SebastianEspende/PROYECTOCNC/3d/v2/agarremotor.SLDPRT

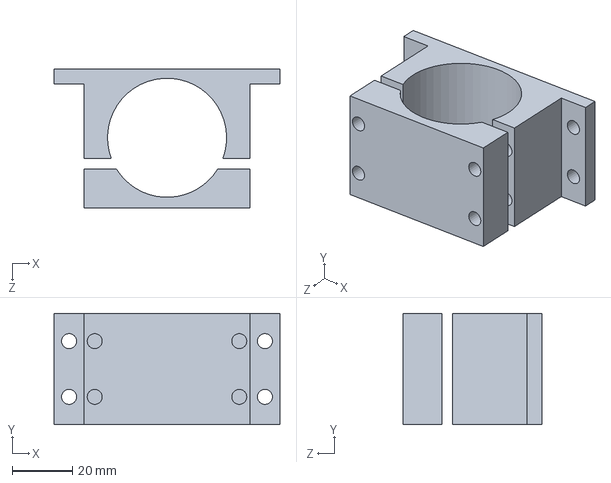
[picture p49: CAD file, 2024-12-08]
3d/v2/agarremotor.SLDPRT
75.0 x 37.0 x 46.2 mm
