SebastianEspende/PROYECTOCNC/3d/Y.SLDPRT

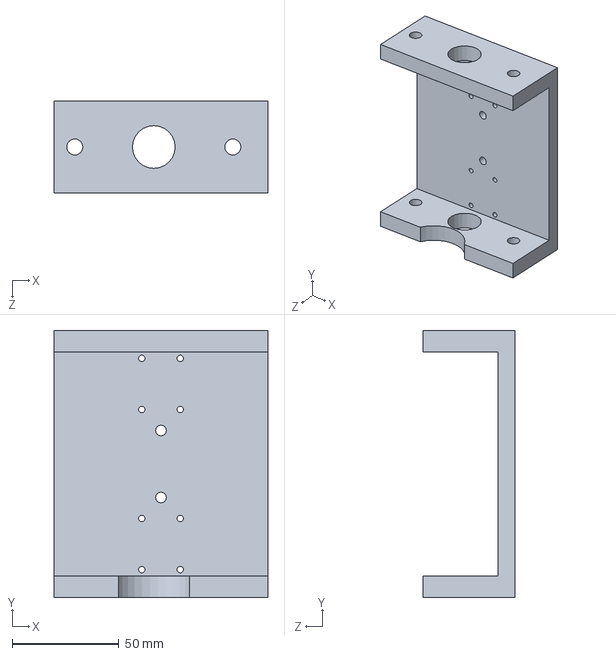
[picture p50: CAD file, 2024-12-08]
3d/Y.SLDPRT
100.0 x 125.0 x 43.0 mm
