SebastianEspende/PROYECTOCNC/3d/FRONTAL_BASE.SLDPRT

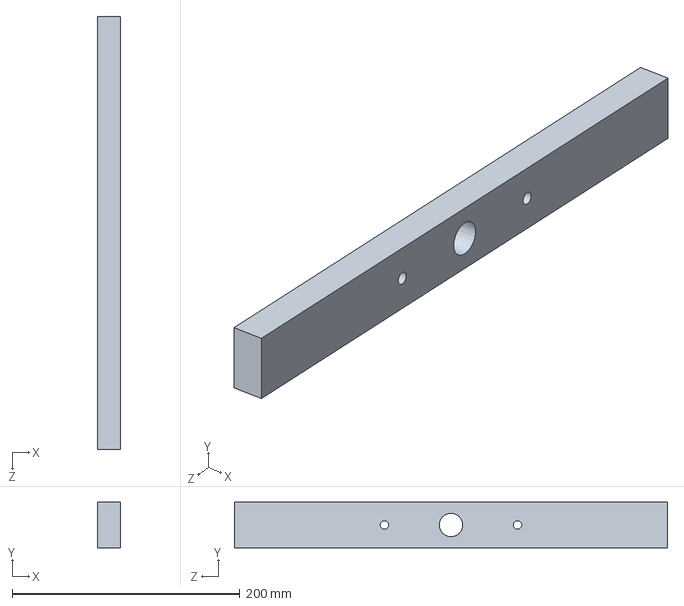
[picture p51: CAD file, 2024-12-08]
3d/FRONTAL_BASE.SLDPRT
20.0 x 40.0 x 380.0 mm
