SebastianEspende/PROYECTOCNC/3d/v2/soportenema17.SLDPRT

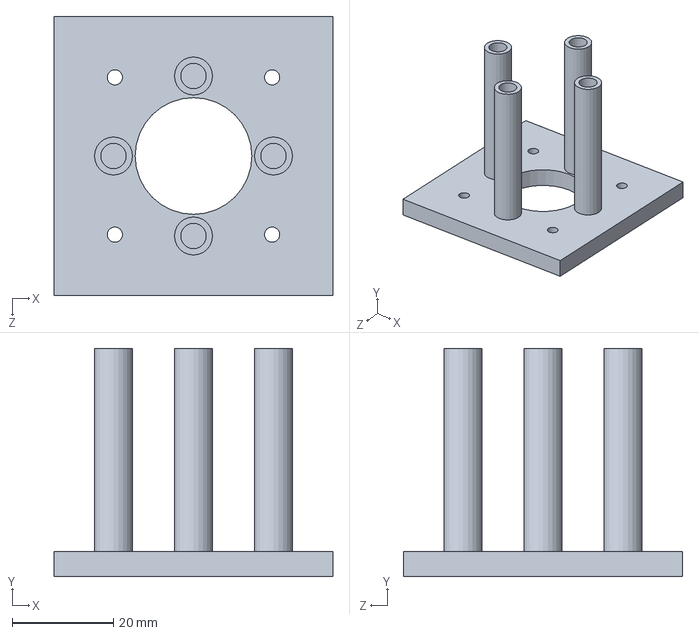
[picture p52: CAD file, 2024-12-08]
3d/v2/soportenema17.SLDPRT
55.0 x 45.0 x 55.0 mm
