SebastianEspende/PROYECTOCNC/3d/BASE.SLDPRT

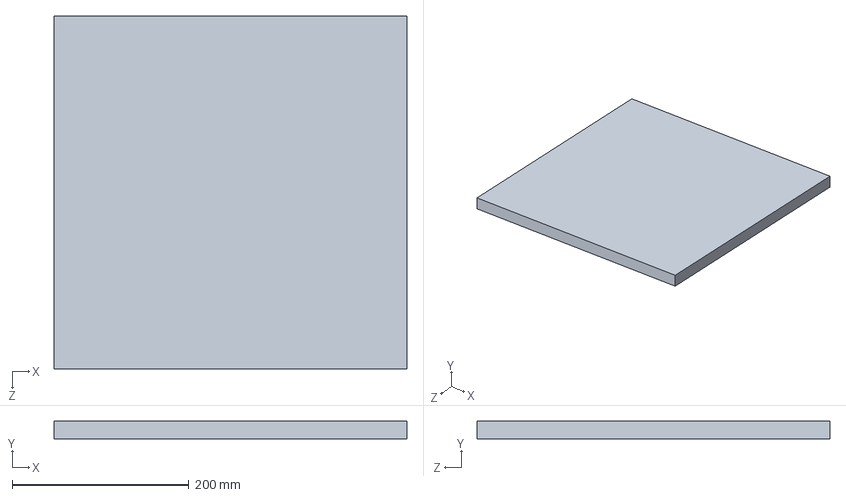
[picture p53: CAD file, 2024-12-04]
3d/BASE.SLDPRT
400.0 x 20.0 x 400.0 mm
