SebastianEspende/PROYECTOCNC/3d/v2/varilla_enroscada_Z.SLDPRT

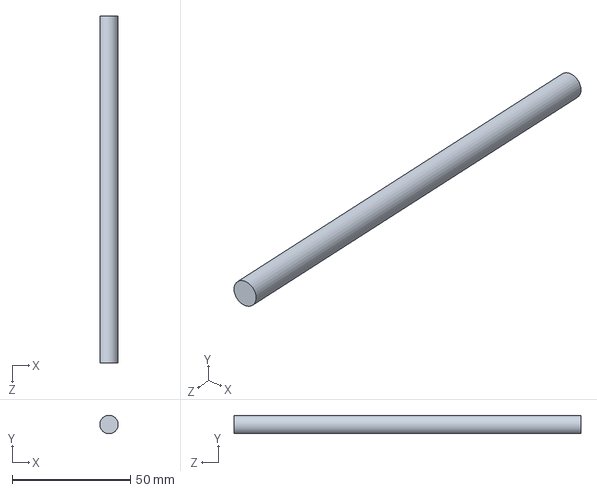
[picture p54: CAD file, 2024-12-08]
3d/v2/varilla_enroscada_Z.SLDPRT
7.80 x 7.76 x 146.5 mm
