SebastianEspende/PROYECTOCNC/3d/GUIA_RAIL_VARILLA.SLDPRT

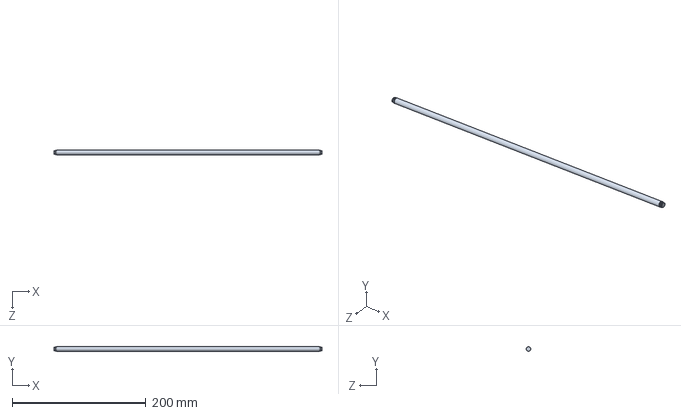
[picture p55: CAD file, 2024-12-04]
3d/GUIA_RAIL_VARILLA.SLDPRT
400.0 x 7.00 x 7.00 mm
