SebastianEspende/PROYECTOCNC/3d/GUIA_LINEAL.SLDPRT

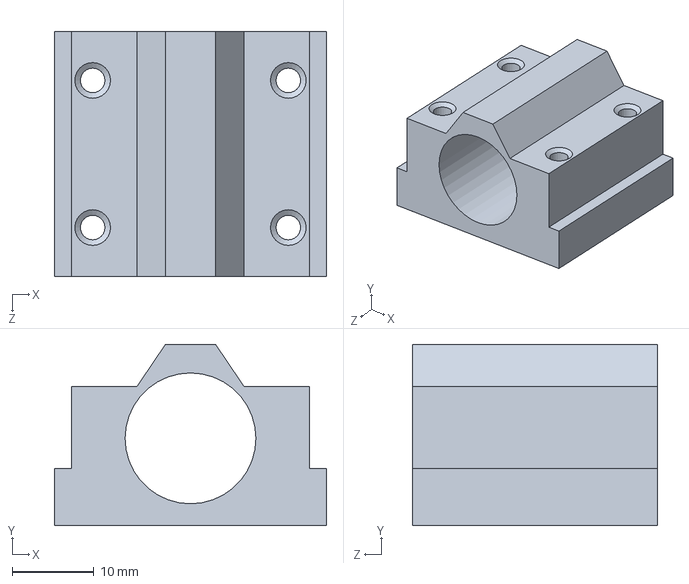
[picture p56: CAD file, 2024-12-04]
3d/GUIA_LINEAL.SLDPRT
33.3 x 22.2 x 30.0 mm
