SebastianEspende/PROYECTOCNC/3d/v2/paso_a_paso.SLDPRT

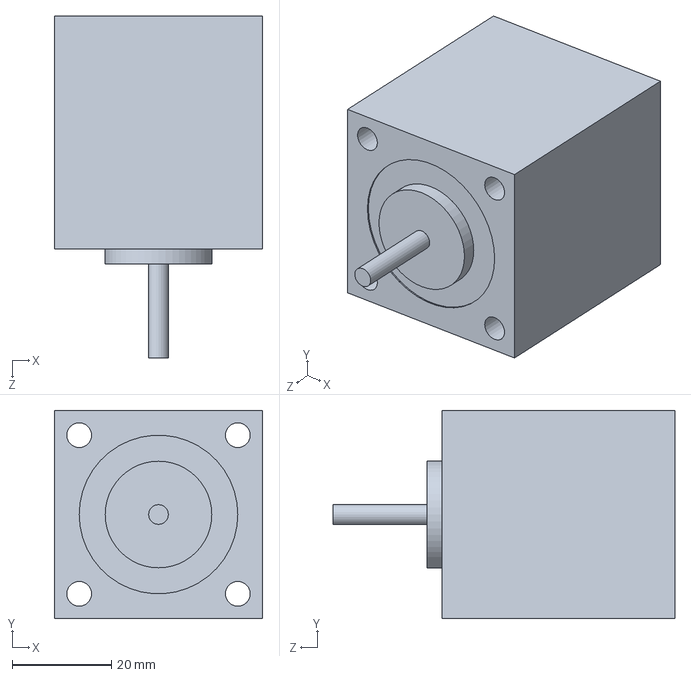
[picture p57: CAD file, 2024-12-04]
3d/v2/paso_a_paso.SLDPRT
42.0 x 42.0 x 69.0 mm
