SebastianEspende/PROYECTOCNC/3d/v2/Part2.SLDPRT

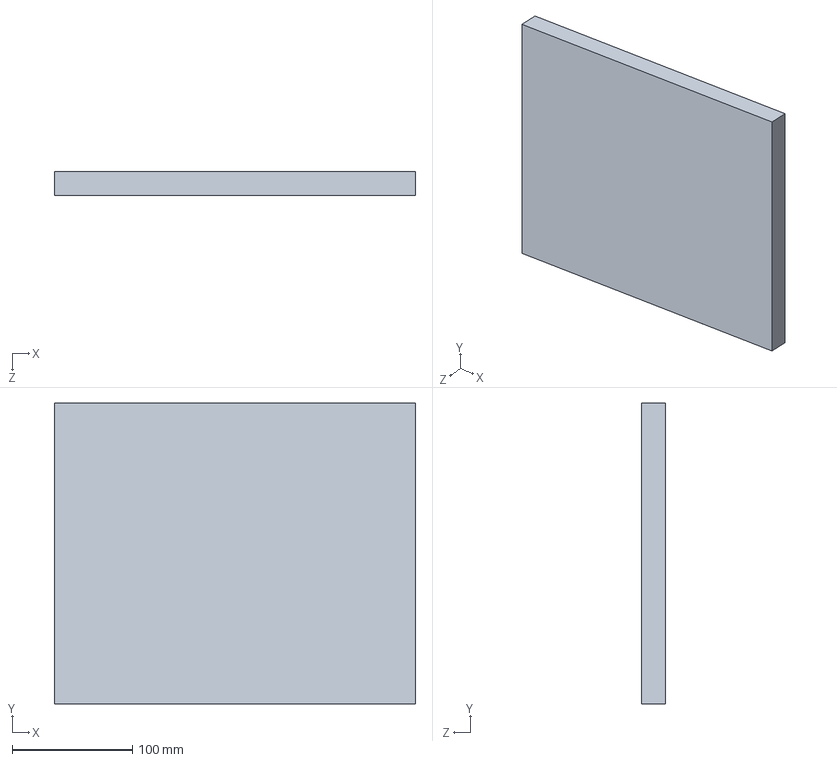
[picture p58: CAD file, 2024-12-04]
3d/v2/Part2.SLDPRT
300.0 x 250.0 x 20.0 mm
