SebastianEspende/PROYECTOCNC/3d/v2/Motor2.SLDPRT

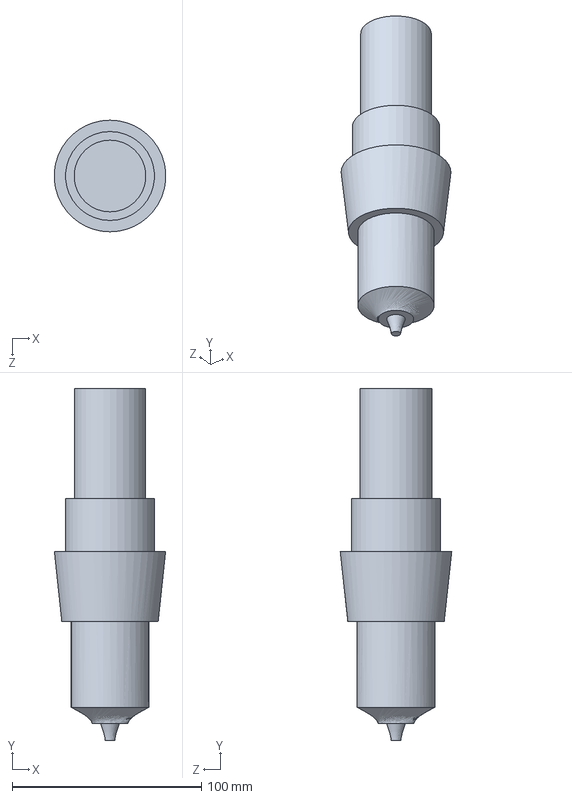
[picture p59: CAD file, 2024-12-04]
3d/v2/Motor2.SLDPRT
58.8 x 186.0 x 59.0 mm
