SebastianEspende/PROYECTOCNC/3d/v2/BASE2.SLDPRT

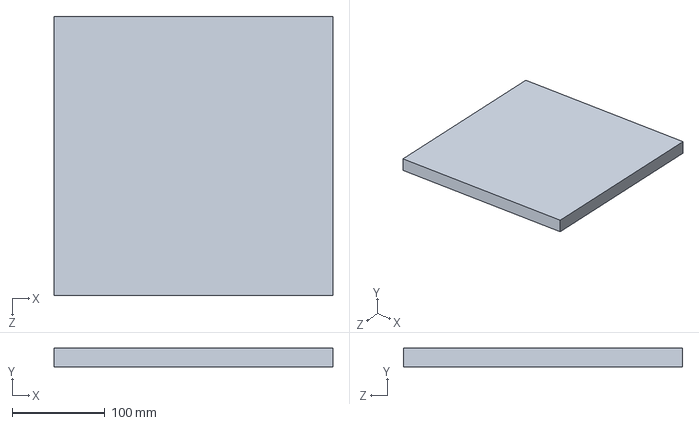
[picture p60: CAD file, 2024-12-04]
3d/v2/BASE2.SLDPRT
300.0 x 20.0 x 300.0 mm
