SebastianEspende/PROYECTOCNC/3d/v2/Motor3.SLDPRT

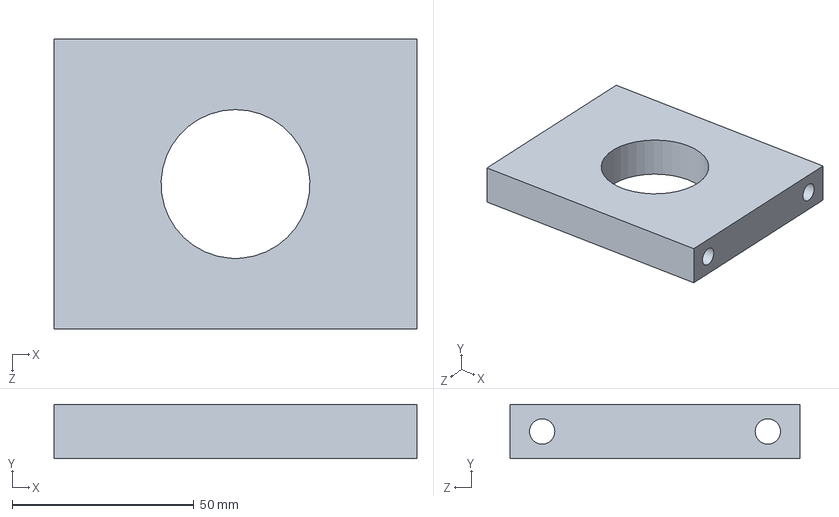
[picture p61: CAD file, 2024-12-04]
3d/v2/Motor3.SLDPRT
100.0 x 15.0 x 80.0 mm
