SebastianEspende/PROYECTOCNC/3d/spindle.SLDPRT

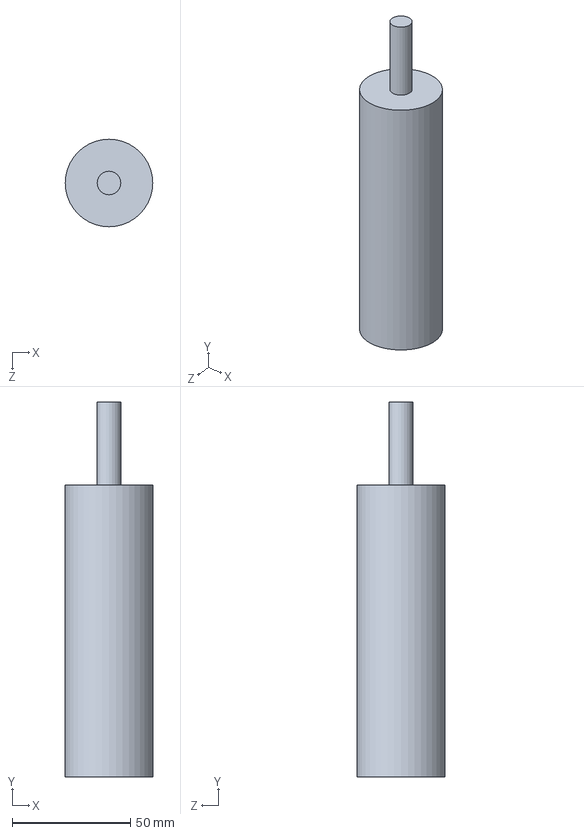
[picture p62: CAD file, 2024-12-04]
3d/spindle.SLDPRT
37.0 x 158.5 x 37.0 mm
