SebastianEspende/PROYECTOCNC/3d/v2/sostenmotor.SLDPRT

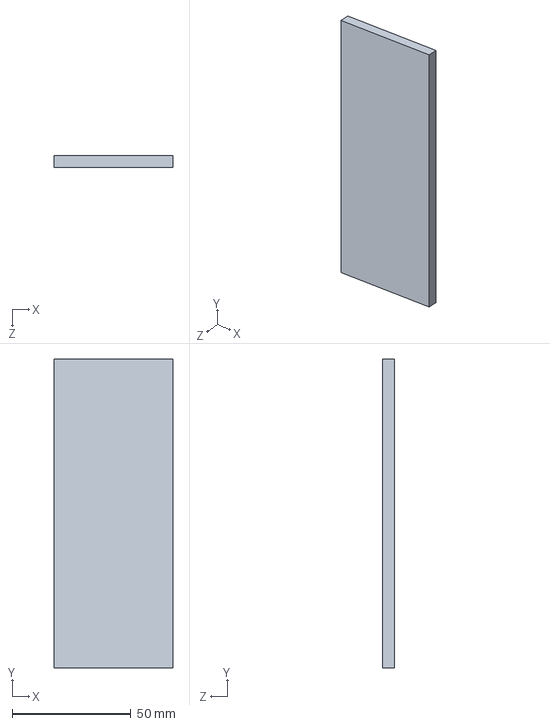
[picture p63: CAD file, 2024-12-04]
3d/v2/sostenmotor.SLDPRT
50.0 x 130.0 x 5.00 mm
