SebastianEspende/PROYECTOCNC/3d/Agarre_motor.SLDPRT

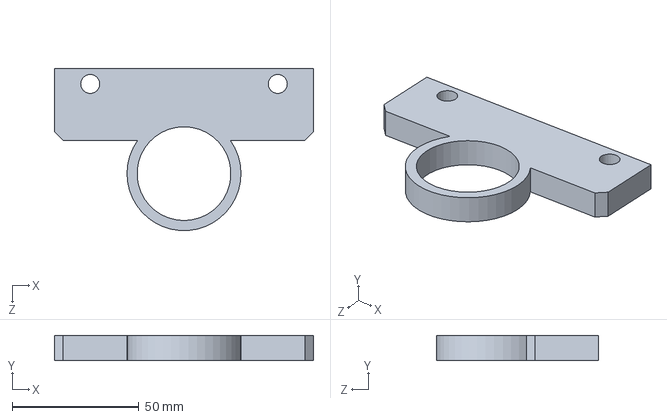
[picture p64: CAD file, 2024-12-04]
3d/Agarre_motor.SLDPRT
102.2 x 10.0 x 63.9 mm
