SebastianEspende/PROYECTOCNC/ARD-MOTORES/ARD-MOTORES2/ARD-MOTORES2.kicad_sch

## KiCad design ARD-MOTORES/ARD-MOTORES2/ARD-MOTORES2.kicad_sch (2024-12-08)

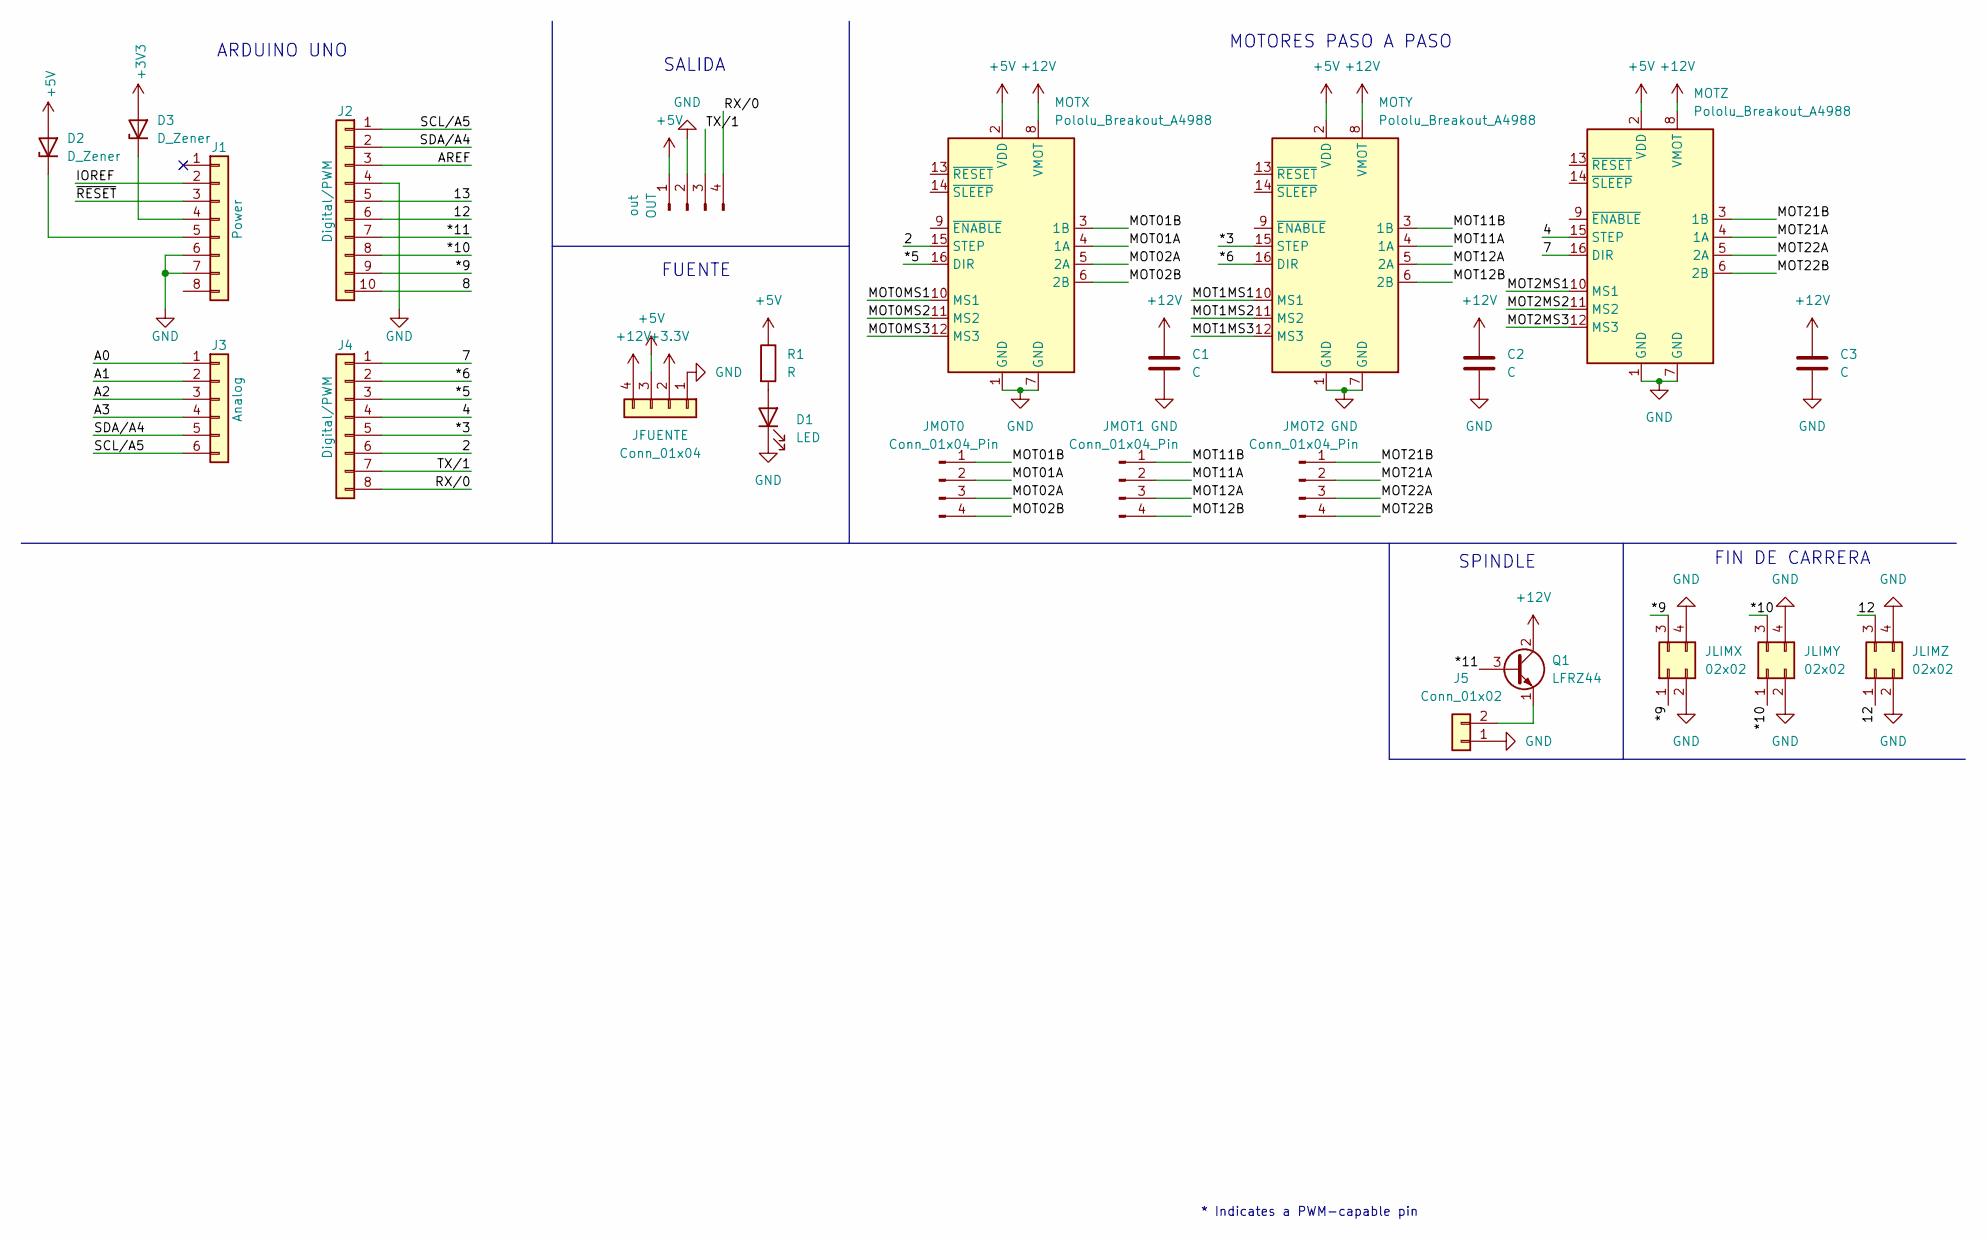
[picture p72: schematic ARD-MOTORES2.kicad_sch]

Parts:
C1, C2, C3: C
D1: LED
D2, D3: D_Zener
J1: Power; PinSocket_1x08_P2.54mm_Vertical
J2: Digital/PWM; PinSocket_1x10_P2.54mm_Vertical
J3: Analog; PinSocket_1x06_P2.54mm_Vertical
J4: Digital/PWM; PinSocket_1x08_P2.54mm_Vertical
J5: Conn_01x02
JFUENTE: Conn_01x04
JLIMX: 02x02
JLIMY: 02x02
JLIMZ: 02x02
JMOT0, JMOT1, JMOT2: Conn_01x04_Pin
MOTX: Pololu_Breakout_A4988; Pololu_Breakout-16_15.2x20.3mm
MOTY: Pololu_Breakout_A4988; Pololu_Breakout-16_15.2x20.3mm
MOTZ: Pololu_Breakout_A4988; Pololu_Breakout-16_15.2x20.3mm
Q1: LFRZ44; TO-126-3_Vertical
R1: R
out: OUT

Connections:
2: J4.6, MOTX.15 (STEP)
3: J4.5, MOTY.15 (STEP)
4: J4.4, MOTZ.15 (STEP)
5: J4.3, MOTX.16 (DIR)
6: J4.2, MOTY.16 (DIR)
7: J4.1, MOTZ.16 (DIR)
8: J2.10
9: J2.9, JLIMX.1, JLIMX.3
10: J2.8, JLIMY.1, JLIMY.3
11: J2.7, Q1.3 (B)
12: J2.6, JLIMZ.1, JLIMZ.3
13: J2.5
+3.3V: JFUENTE.2
+3V3: D3.2 (A)
+5V: D2.2 (A), JFUENTE.3, MOTX.2 (VDD), MOTY.2 (VDD), MOTZ.2 (VDD), R1.1, out.1
+12V: C1.1, C2.1, C3.1, JFUENTE.4, MOTX.8 (VMOT), MOTY.8 (VMOT), MOTZ.8 (VMOT), Q1.2 (C)
A0: J3.1
A1: J3.2
A2: J3.3
A3: J3.4
AREF: J2.3
GND: C1.2, C2.2, C3.2, D1.1 (K), J1.6, J1.7, J2.4, J5.1, JFUENTE.1, JLIMX.2, JLIMX.4, JLIMY.2, JLIMY.4, JLIMZ.2, JLIMZ.4, MOTX.1 (GND), MOTX.7 (GND), MOTY.1 (GND), MOTY.7 (GND), MOTZ.1 (GND), MOTZ.7 (GND), out.2
IOREF: J1.2
MOT0MS1: MOTX.10 (MS1)
MOT0MS2: MOTX.11 (MS2)
MOT0MS3: MOTX.12 (MS3)
MOT01A: JMOT0.2, MOTX.4 (1A)
MOT01B: JMOT0.1, MOTX.3 (1B)
MOT1MS1: MOTY.10 (MS1)
MOT1MS2: MOTY.11 (MS2)
MOT1MS3: MOTY.12 (MS3)
MOT02A: JMOT0.3, MOTX.5 (2A)
MOT02B: JMOT0.4, MOTX.6 (2B)
MOT2MS1: MOTZ.10 (MS1)
MOT2MS2: MOTZ.11 (MS2)
MOT2MS3: MOTZ.12 (MS3)
MOT11A: JMOT1.2, MOTY.4 (1A)
MOT11B: JMOT1.1, MOTY.3 (1B)
MOT12A: JMOT1.3, MOTY.5 (2A)
MOT12B: JMOT1.4, MOTY.6 (2B)
MOT21A: JMOT2.2, MOTZ.4 (1A)
MOT21B: JMOT2.1, MOTZ.3 (1B)
MOT22A: JMOT2.3, MOTZ.5 (2A)
MOT22B: JMOT2.4, MOTZ.6 (2B)
unnamed: D1.2 (A), R1.2
unnamed: D2.1 (K), J1.5
unnamed: D3.1 (K), J1.4
unnamed: J5.2, Q1.1 (E)
RX/0: J4.8, out.4
SCL/A5: J2.1, J3.6
SDA/A4: J2.2, J3.5
TX/1: J4.7, out.3
~RESET: J1.3

Notes on the sheet:
ARDUINO UNO
FUENTE
MOTORES PASO A PASO
* Indicates a PWM-capable pin
SALIDA
SPINDLE
FIN DE CARRERA
